BertCox/class-d-amp/Simulation/amp_saver.asc

C1: cap; 820p
R1: res; 2.2k
R2: res; 2.2k
R3: res; 10k
R4: res; 1k
R5: res; 30k
U1: LT1011
U2: LT1011
V1: voltage; PULSE(0 24 40u 1n 1n 2u 4u 12)
V2: voltage; 24
Named nets: 0, clkpres, clk, filt
.tran 0 120u 0 10n
